kushalgollen/DIY-Benchtop-Power-Supply-Unit/docs/images/func_2.jpeg

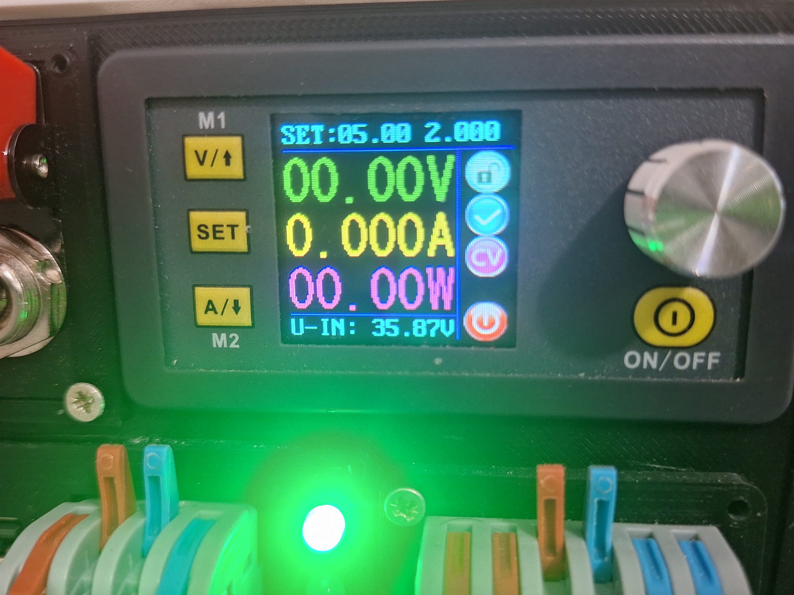
docs/images/func_2.jpeg
