kushalgollen/DIY-Benchtop-Power-Supply-Unit/docs/images/image_2.jpeg

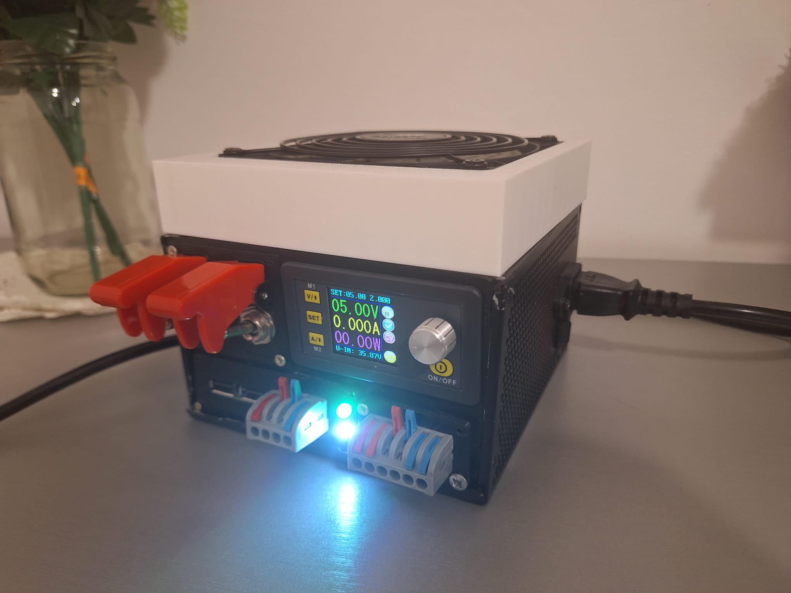
docs/images/image_2.jpeg
