kushalgollen/DIY-Benchtop-Power-Supply-Unit/docs/images/image_3.png

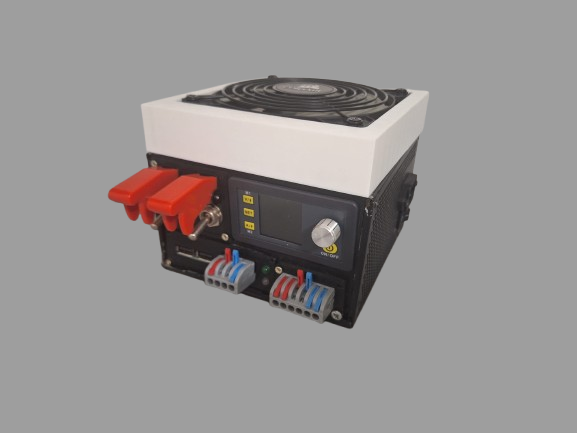
docs/images/image_3.png
