kushalgollen/DIY-Benchtop-Power-Supply-Unit/docs/images/internel_3.jpeg

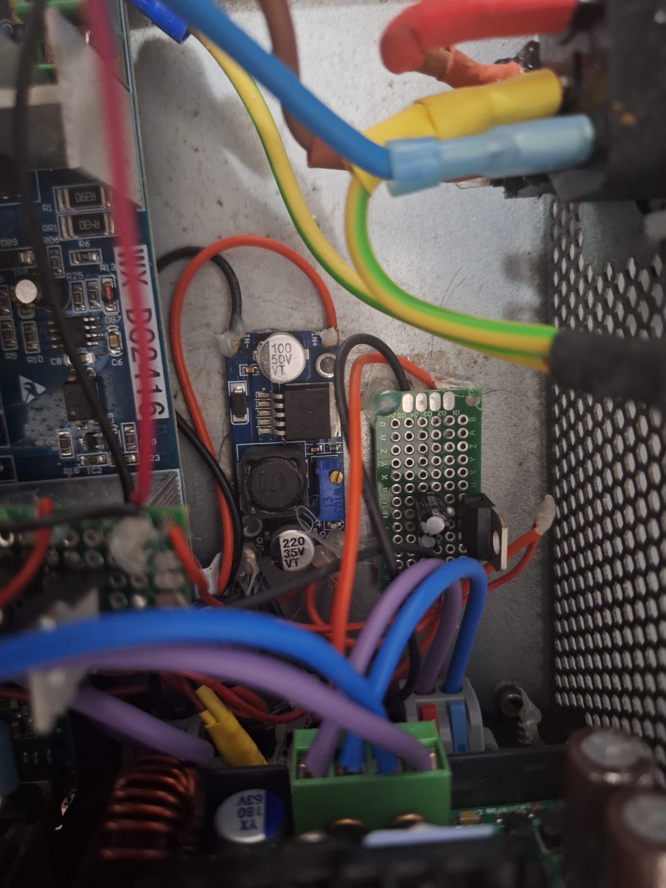
docs/images/internel_3.jpeg
